LaboratorioGluon/Solar-Scavenger/3D/Casco_barco_v0.FCStd

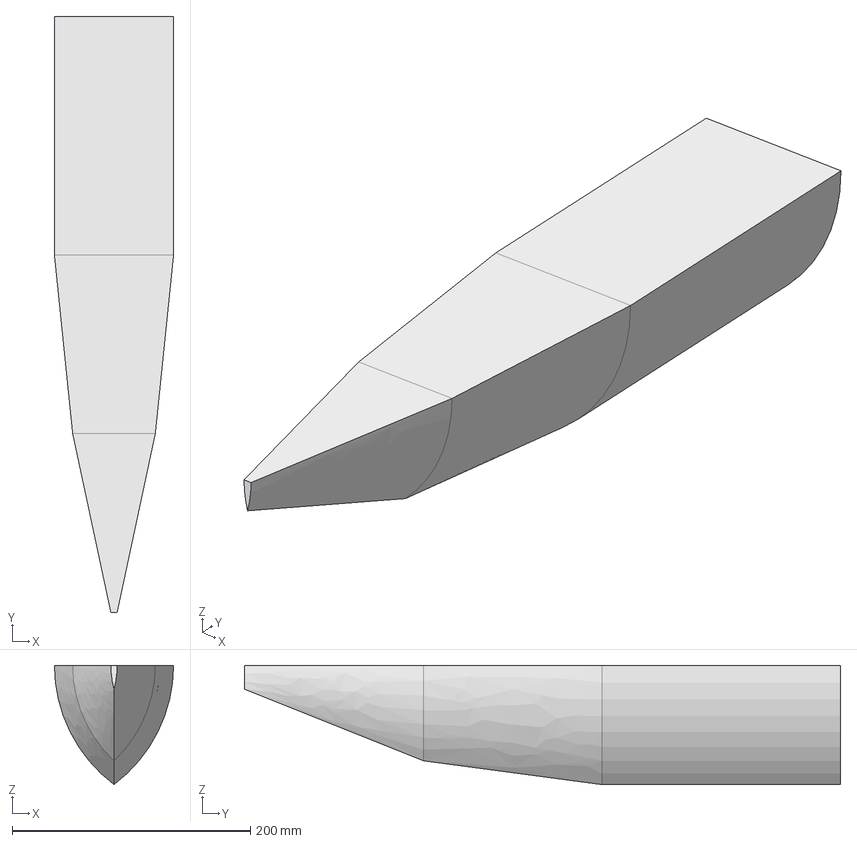
[picture p17: CAD file, 2023-02-12]
3D/Casco_barco_v0.FCStd
100.0 x 500.0 x 100.0 mm
