LaboratorioGluon/Solar-Scavenger/3D/stls/Direccion_sg90-AletaSoporte.stl

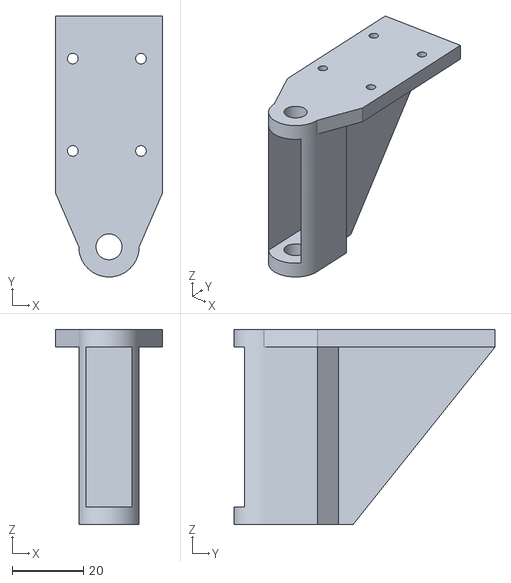
[picture p18: CAD file, 2023-02-12]
3D/stls/Direccion_sg90-AletaSoporte.stl
30.0 x 73.5 x 55.0
