LaboratorioGluon/Solar-Scavenger/3D/stls/Casco_barco/Casco3.stl

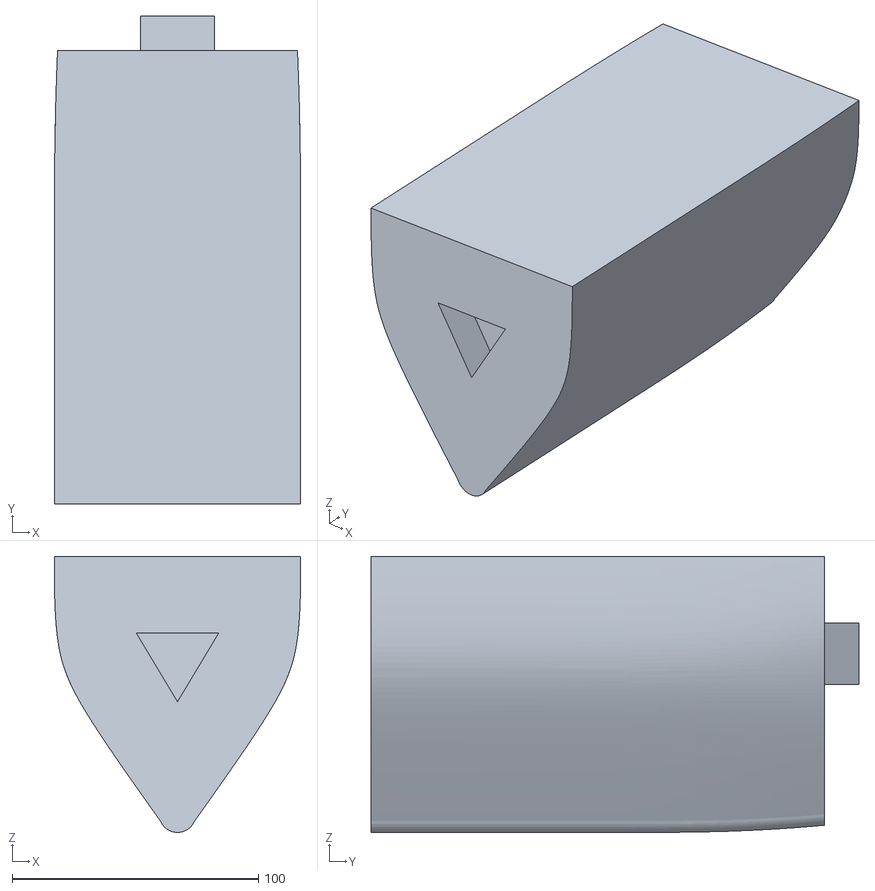
[picture p19: CAD file, 2023-02-22]
3D/stls/Casco_barco/Casco3.stl
100.0 x 198.0 x 112.0
