LaboratorioGluon/Solar-Scavenger/3D/stls/Hull_frontal.stl

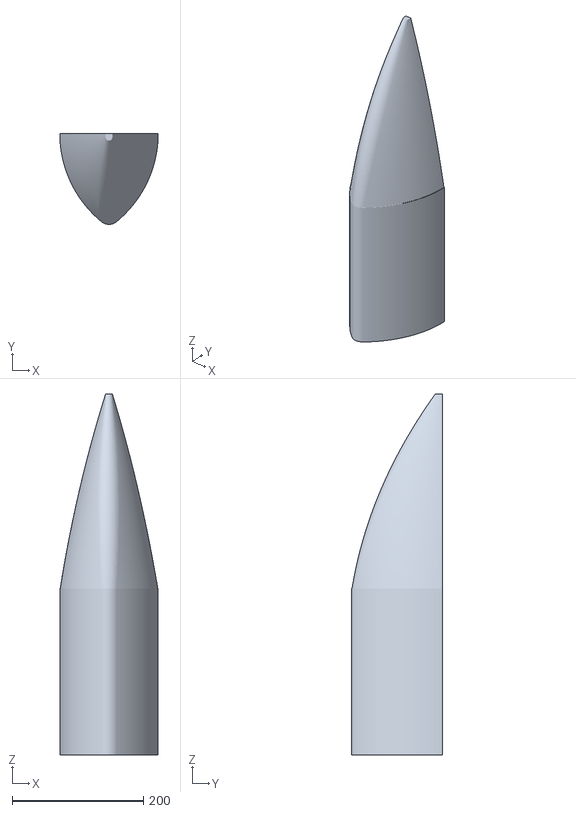
[picture p20: CAD file, 2023-02-12]
3D/stls/Hull_frontal.stl
150.0 x 138.3 x 550.0
