LaboratorioGluon/Solar-Scavenger/3D/stls/Test_Soporte_Servo.stl

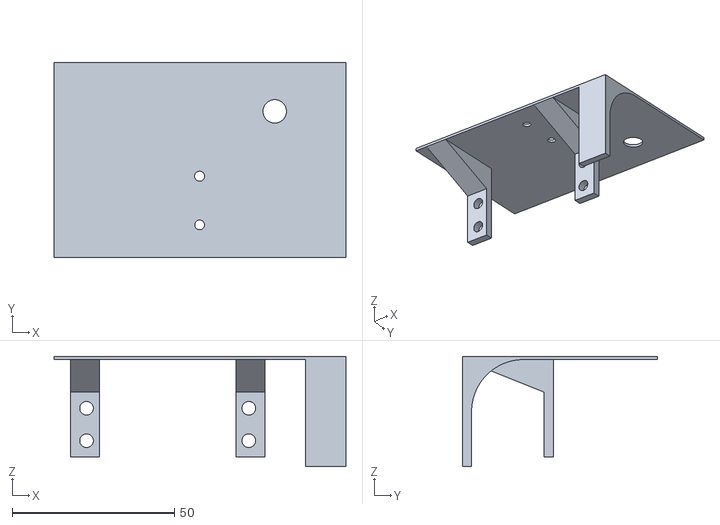
[picture p21: CAD file, 2023-02-12]
3D/stls/Test_Soporte_Servo.stl
90.0 x 60.0 x 34.0
