LaboratorioGluon/Solar-Scavenger/3D/stls/Test_Soporte_Barra.stl

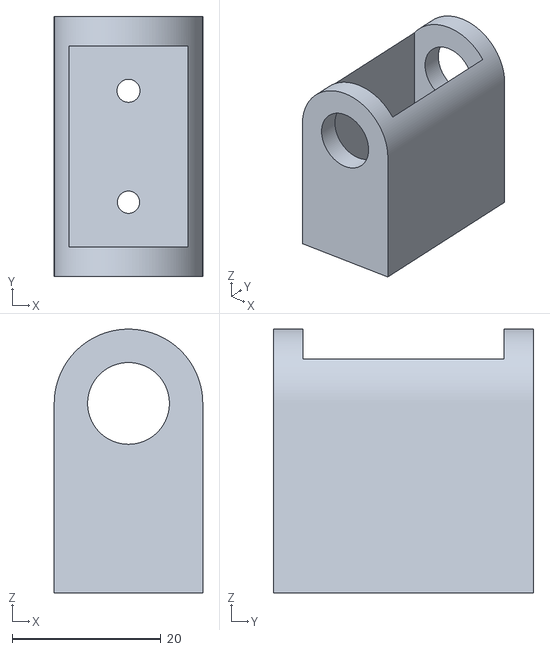
[picture p22: CAD file, 2023-02-12]
3D/stls/Test_Soporte_Barra.stl
20.0 x 35.0 x 35.5
