LaboratorioGluon/Solar-Scavenger/3D/stls/Direccion_sg90-Body_v2.stl

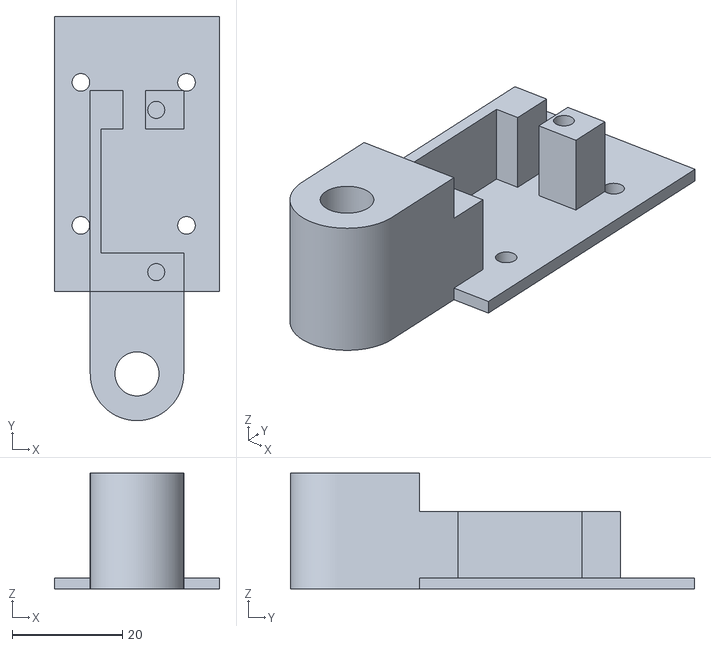
[picture p23: CAD file, 2023-02-12]
3D/stls/Direccion_sg90-Body_v2.stl
30.0 x 73.5 x 21.0
