LaboratorioGluon/Solar-Scavenger/3D/stls/Direccion_sg90-Body.stl

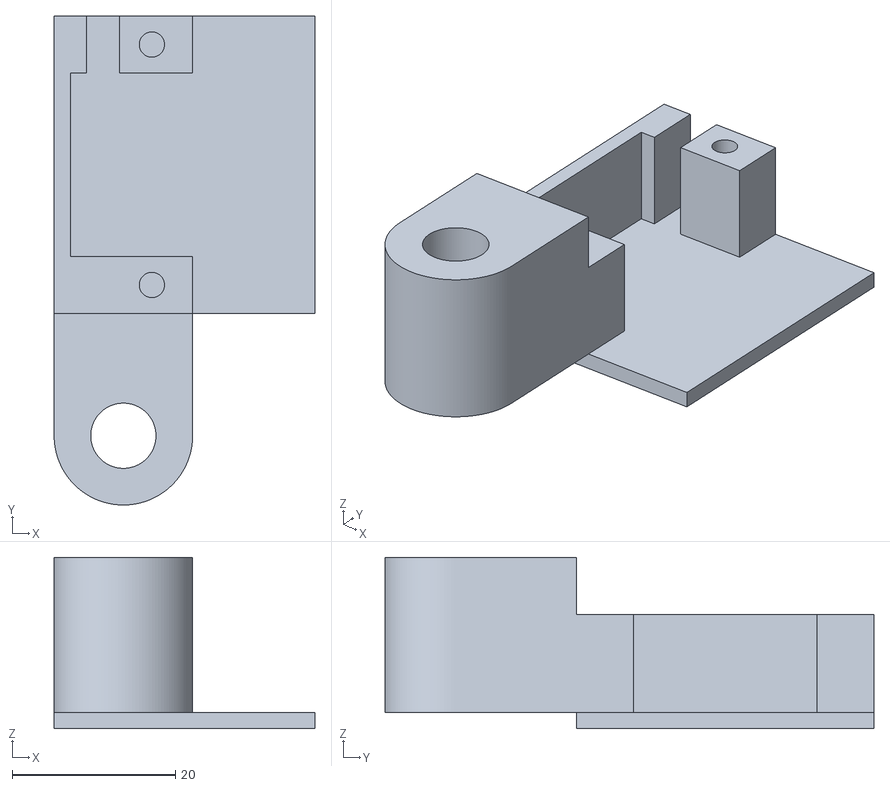
[picture p24: CAD file, 2023-02-12]
3D/stls/Direccion_sg90-Body.stl
32.0 x 60.0 x 21.0
